j0of/flappybird32/include/Obstacle.h

#pragma once

#include <Adafruit_ST7735.h>
#include "Player.h"

class ObstacleManager;

class Obstacle {
    friend class ObstacleManager;
public:
    Obstacle(Adafruit_ST7735 *_tft, int _x = 0);
private:
    void reset(int _x);

    void tick(float dt);
    void clear() const;
    void draw() const;

    Adafruit_ST7735 *tft;

    static constexpr int w = 25;
    float x;
    int y2;
    int h1, h2;
    bool scored;

    static constexpr int y1 = 0;
    static constexpr int speed = 80;
    static constexpr int yGap = 50;
};
